elcesarlokuelo/Gaita_electronica_MIDI/1_FCStd/caja_sup.FCStd

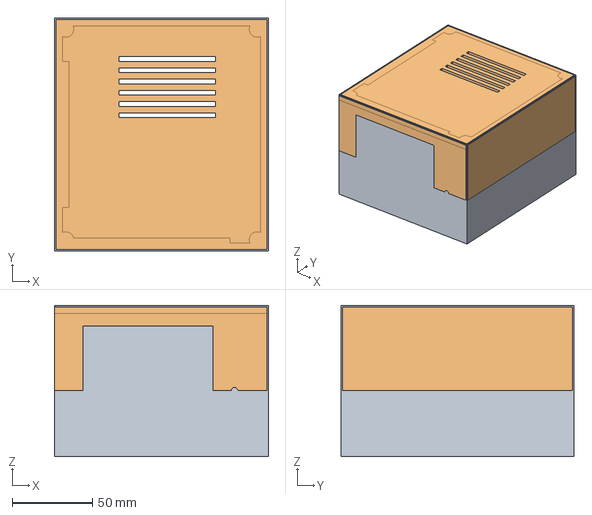
[picture p110: CAD file, 2024-06-26]
1_FCStd/caja_sup.FCStd
133.1 x 145.0 x 94.0 mm
Cuerpo
