elcesarlokuelo/Gaita_electronica_MIDI/1_FCStd/tuerca2.FCStd

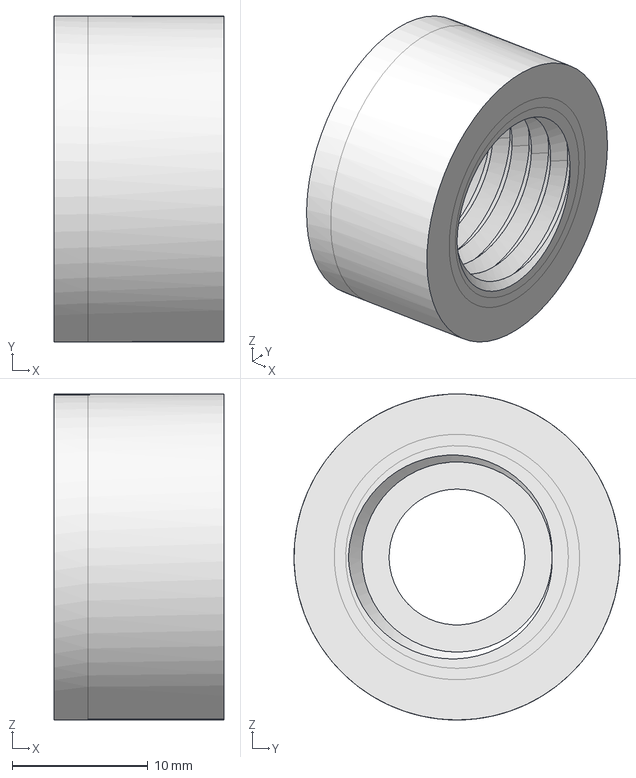
[picture p111: CAD file, 2024-06-26]
1_FCStd/tuerca2.FCStd
12.5 x 24.0 x 24.0 mm
